wimberlyw/ardumiibo/Game/TurboWaddle/characters.h

 //this contains the sprite arrays
#include <Arduboy2.h>

// IMAGES FOR RUNNING MAN

const uint8_t PROGMEM runningman[] = 
{
  16,16,
  //FRAME 1
  0x00, 0x00, 0xc0, 0xe0, 0x70, 0x30, 0x30, 0x30, 0xe0, 0xe0, 0xfc, 0x3c, 0x34, 0xbc, 0xc0, 0xc0, 
  0x0c, 0x1c, 0x38, 0x30, 0x30, 0x38, 0x1c, 0x0e, 0x07, 0x03, 0x0f, 0x1f, 0x3b, 0x71, 0xe1, 0xc0, 
   //FRAME 2
  0x00, 0x00, 0x00, 0x00, 0x00, 0xe0, 0xf0, 0xb0, 0xf0, 0xfc, 0x3c, 0xb4, 0xbc, 0x00, 0x00, 0x00, 
  0x00, 0x00, 0x00, 0x18, 0x38, 0x30, 0x39, 0x1d, 0x0f, 0x07, 0x0f, 0x1f, 0xf9, 0xf0, 0x00, 0x00, 
   //FRAME 3
  0x00, 0x00, 0x00, 0x00, 0x00, 0x00, 0x80, 0xc0, 0xfc, 0xfc, 0xb4, 0x3c, 0x00, 0x00, 0x00, 0x00, 
  0x00, 0x00, 0x00, 0x00, 0x00, 0x00, 0x00, 0x01, 0xff, 0xff, 0x7b, 0x33, 0x00, 0x00, 0x00, 0x00, 
   //FRAME 4
  0x00, 0x00, 0x00, 0x00, 0xc0, 0xe0, 0x70, 0x30, 0xf0, 0xfc, 0x3c, 0xb4, 0xfc, 0xc0, 0x00, 0x00, 
  0x00, 0x00, 0xc0, 0xe0, 0x70, 0x38, 0x1c, 0x0e, 0x07, 0x03, 0x03, 0x07, 0x0f, 0x1c, 0x38, 0x60, 
  //JUMP FRAME
  0x00, 0x00, 0x00, 0x00, 0x00, 0x00, 0x00, 0x80, 0xe0, 0xf0, 0xfc, 0x7f, 0x37, 0x3e, 0x07, 0x03, 
  0x30, 0x38, 0x1c, 0xcc, 0xee, 0x77, 0x3b, 0x1f, 0x0f, 0x07, 0x01, 0x00, 0x00, 0x00, 0x00, 0x00, 
};

const uint8_t PROGMEM beefball[] = 
{
  16, 16,
  //FRAME 1
  0x00, 0x40, 0x80, 0xd0, 0xe0, 0x60, 0x20, 0x20, 0xb0, 0x20, 0x60, 0x60, 0xc0, 0xa0, 0x00, 0x00, 
  0x84, 0x7f, 0xff, 0xc1, 0x80, 0x84, 0x8e, 0x98, 0x91, 0x90, 0x8b, 0x80, 0xc0, 0xe1, 0x3f, 0x48, 
  //FRAME 2
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
};

class PlayerOne
{

  public:
    //Vars
    String selectedChar;
    int posY;
    int posX;
    int shield;
    int animStep;
    bool canJump;
    
    //Functions
    PlayerOne(void);
    const uint8_t PROGMEM *getSpriteSet(String);

   
    
};
