wimberlyw/ardumiibo/Game/TurboWaddle/menus.h

#include <Arduboy2.h>


const uint8_t PROGMEM intro[] = {
  64, 32,
  0x80, 0xc0, 0xe0, 0x60, 0x70, 0x30, 0x30, 0x30, 0x70, 0xf0, 0xf0, 0xf0, 0x30, 0x38, 0x18, 0x18, 0x18, 0x18, 0x1c, 0x0c, 0x0c, 0x40, 0xc0, 0xc0, 0x00, 0x00, 0xf0, 0xf8, 0xdc, 0xcc, 0xfc, 0xfc, 0x98, 0x80, 0x00, 0x06, 0x1f, 0x7f, 0xf3, 0xe3, 0x73, 0x3f, 0x3e, 0x30, 0x70, 0xf0, 0xe0, 0x00, 0xf0, 0xfe, 0xfe, 0x0e, 0x86, 0x86, 0xfe, 0xfe, 0x7c, 0x00, 0x80, 0x80, 0x00, 0x00, 0x00, 0x00, 
  0x03, 0x07, 0x0e, 0x0e, 0x0f, 0x07, 0x00, 0x00, 0x00, 0x00, 0x03, 0x07, 0x1f, 0x7c, 0xf0, 0xc0, 0x03, 0x1f, 0x1e, 0xb8, 0xb0, 0xb0, 0xb1, 0x3f, 0x1f, 0x00, 0x00, 0x83, 0x87, 0x9f, 0x9c, 0x80, 0x81, 0x83, 0x87, 0x86, 0x00, 0x70, 0xf3, 0xf7, 0xf7, 0x36, 0x36, 0x76, 0x67, 0xe7, 0xc3, 0xb0, 0x70, 0xf3, 0xc3, 0x03, 0x03, 0x1b, 0x39, 0x7c, 0xee, 0xe7, 0xf3, 0x3b, 0x38, 0x18, 0x00, 0x00, 
  0x00, 0x80, 0xc0, 0xe0, 0xe0, 0x60, 0xe0, 0xc0, 0x00, 0x00, 0x00, 0x00, 0x00, 0x00, 0x0c, 0x1c, 0x3c, 0xf8, 0xe0, 0x8f, 0x3f, 0xff, 0xe3, 0xc7, 0xde, 0xfc, 0x70, 0xe1, 0xe7, 0x8f, 0x19, 0x71, 0xe1, 0xc1, 0x83, 0x87, 0xff, 0xfc, 0xf0, 0x03, 0x0f, 0x1e, 0x78, 0xe0, 0xc0, 0xe0, 0x7f, 0x3f, 0x00, 0x03, 0x07, 0x1f, 0xfc, 0xf0, 0xe0, 0x70, 0x70, 0x33, 0x07, 0x1e, 0x1c, 0x1c, 0x0f, 0x07, 
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
    void CharacterSelect(Arduboy2, String *characters, bool *unlocks, int, int);
    bool ScanMenu(Arduboy2 ab, String *characters, bool *unlocks, int x, int y);
    bool openEgg(Arduboy2 ab, int x, int y);
    int swoosValue(int frame, bool negative);
};
