wimberlyw/ardumiibo/Scanner Programs/NFCReader/NFCReader.ino

#include <Wire.h>

#include <PN532_I2C.h>

#include <PN532.h>

#include <NfcAdapter.h>
PN532_I2C pn532_i2c(Wire);

#include <Adafruit_NeoPixel.h>
#define LED_PIN    4
#define LED_COUNT 24




String finalpayload = "";

NfcAdapter nfc = NfcAdapter(pn532_i2c);

Adafruit_NeoPixel strip(LED_COUNT, LED_PIN, NEO_GRB + NEO_KHZ800);
// Argument 1 = Number of pixels in NeoPixel strip
// Argument 2 = Arduino pin number (most are valid)
// Argument 3 = Pixel type flags, add together as needed:
//   NEO_KHZ800  800 KHz bitstream (most NeoPixel products w/WS2812 LEDs)
//   NEO_KHZ400  400 KHz (classic 'v1' (not v2) FLORA pixels, WS2811 drivers)
//   NEO_GRB     Pixels are wired for GRB bitstream (most NeoPixel products)
//   NEO_RGB     Pixels are wired for RGB bitstream (v1 FLORA pixels, not v2)
//   NEO_RGBW    Pixels are wired for RGBW bitstream (NeoPixel RGBW products)

String Message;

void setup() {
  
  Serial1.begin(115200);
  delay(100);
  nfc.begin();
  //Serial1.println("on");
  delay(1000);
  //Serial1.println("Scan your Arduumiibo");
  //delay(3000);
  strip.begin();           // INITIALIZE NeoPixel strip object (REQUIRED)
  strip.show();            // Turn OFF all pixels ASAP
  strip.setBrightness(50); // Set BRIGHTNESS to about 1/5 (max = 255)
}

void loop() {
    
    theaterChase(strip.Color(  0,   0, 127), 50); // Blue, half brightness
    if (nfc.tagPresent())
    {
       NfcTag tag = nfc.read();
    if (tag.hasNdefMessage()) // If your tag has a message
    {

      NdefMessage message = tag.getNdefMessage();
      /*Serial.print("\nThis Message in this Tag is ");
      Serial.print(message.getRecordCount());
      Serial.print(" NFC Tag Record");
      if (message.getRecordCount() != 1) { 
        //Serial.print("s");
      }
      Serial.println(".");
      */
      // If you have more than 1 Message then it wil cycle through them
      int recordCount = message.getRecordCount();
      for (int i = 0; i < recordCount; i++)
      {
        Serial.print("\nNDEF Record ");Serial.println(i+1);
        NdefRecord record = message.getRecord(i);

        int payloadLength = record.getPayloadLength();
        byte payload[payloadLength];
        record.getPayload(payload);


        String payloadAsString = ""; // Processes the message as a string vs as a HEX value
        
        for (int c = 0; c < payloadLength; c++) {
          
          payloadAsString += (char)payload[c];
          
          
          
        }
        //Serial.print("  Information (as String): ");
        
        Serial1.println(payloadAsString);
        colorWipe(strip.Color(  0, 255,   0), 50); // Green
        delay(500);
        theaterChase(strip.Color(  0,   127, 0), 25); // green, half brightness
        rainbow(3);             // Flowing rainbow cycle along the whole strip
        delay(1000);            //duration 2 seconds
       // Serial1.println("Ending Link");
        delay(1000);
        Serial1.flush();
        
        //Serial1.println("off");
        //Serial1.end();
/*
        String uid = record.getId();
        if (uid != "") {
          Serial.print("  ID: ");Serial.println(uid); // Prints the Unique Identification of the NFC Tag
        }*/
      }
    }
 }
}

// Some functions of our own for creating animated effects -----------------

// Fill strip pixels one after another with a color. Strip is NOT cleared
// first; anything there will be covered pixel by pixel. Pass in color
// (as a single 'packed' 32-bit value, which you can get by calling
// strip.Color(red, green, blue) as shown in the loop() function above),
// and a delay time (in milliseconds) between pixels.
void colorWipe(uint32_t color, int wait) {
  for (int i = 0; i < strip.numPixels(); i++) { // For each pixel in strip...
    strip.setPixelColor(i, color);         //  Set pixel's color (in RAM)
    strip.show();                          //  Update strip to match
    delay(wait);                           //  Pause for a moment
  }
}

// Theater-marquee-style chasing lights. Pass in a color (32-bit value,
// a la strip.Color(r,g,b) as mentioned above), and a delay time (in ms)
// between frames.
void theaterChase(uint32_t color, int wait) {
  for (int a = 0; a < 10; a++) { // Repeat 10 times...
    for (int b = 0; b < 3; b++) { //  'b' counts from 0 to 2...
      strip.clear();         //   Set all pixels in RAM to 0 (off)
      // 'c' counts up from 'b' to end of strip in steps of 3...
      for (int c = b; c < strip.numPixels(); c += 3) {
        strip.setPixelColor(c, color); // Set pixel 'c' to value 'color'
      }
      strip.show(); // Update strip with new contents
      delay(wait);  // Pause for a moment
    }
  }
}

// Rainbow cycle along whole strip. Pass delay time (in ms) between frames.
void rainbow(int wait) {
  // Hue of first pixel runs 5 complete loops through the color wheel.
  // Color wheel has a range of 65536 but it's OK if we roll over, so
  // just count from 0 to 5*65536. Adding 256 to firstPixelHue each time
  // means we'll make 5*65536/256 = 1280 passes through this outer loop:
  for (long firstPixelHue = 0; firstPixelHue < 5 * 65536; firstPixelHue += 256) {
    for (int i = 0; i < strip.numPixels(); i++) { // For each pixel in strip...
      // Offset pixel hue by an amount to make one full revolution of the
      // color wheel (range of 65536) along the length of the strip
      // (strip.numPixels() steps):
      int pixelHue = firstPixelHue + (i * 65536L / strip.numPixels());
      // strip.ColorHSV() can take 1 or 3 arguments: a hue (0 to 65535) or
      // optionally add saturation and value (brightness) (each 0 to 255).
      // Here we're using just the single-argument hue variant. The result
      // is passed through strip.gamma32() to provide 'truer' colors
      // before assigning to each pixel:
      strip.setPixelColor(i, strip.gamma32(strip.ColorHSV(pixelHue)));
    }
    strip.show(); // Update strip with new contents
    delay(wait);  // Pause for a moment
  }
}
