wimberlyw/ardumiibo/Examples/ScanDemo/sprites.h

#pragma once

const uint8_t PROGMEM GL0[] = {
32, 32,
0x00, 0x00, 0x00, 0xc0, 0xb0, 0x50, 0x1c, 0x0e, 0x82, 0x22, 0xb2, 0x02, 0x02, 0x02, 0x04, 0x08, 0x08, 0xf0, 0x80, 0x00, 0x00, 0x00, 0x00, 0x00, 0x00, 0x00, 0x00, 0x00, 0x00, 0x00, 0x00, 0x00, 
0x80, 0x40, 0x80, 0x41, 0x46, 0x40, 0x45, 0x7d, 0x7d, 0x1d, 0x01, 0x81, 0x01, 0x00, 0x04, 0xde, 0xde, 0xfa, 0xf8, 0xd7, 0xc0, 0xbc, 0x20, 0xc0, 0x00, 0x00, 0x00, 0x00, 0x00, 0x00, 0x00, 0x00, 
0x07, 0x08, 0x0b, 0x1c, 0x14, 0xe8, 0x08, 0x08, 0x08, 0x08, 0x8c, 0x03, 0x00, 0x00, 0x00, 0x01, 0x01, 0x0b, 0xf7, 0xf5, 0x25, 0x03, 0x7c, 0x83, 0x00, 0x00, 0x00, 0x00, 0x00, 0x00, 0x00, 0x00, 
0x00, 0x00, 0x00, 0x00, 0x00, 0x01, 0xc6, 0x24, 0xba, 0xc1, 0x00, 0x00, 0x00, 0xc2, 0xf8, 0xc0, 0xc0, 0x80, 0x80, 0x8e, 0x1d, 0x1a, 0x08, 0x21, 0x36, 0x28, 0x38, 0x30, 0xe0, 0x00, 0x00, 0x00, 

0x00, 0x00, 0x00, 0xc0, 0xb0, 0x50, 0x1c, 0x0e, 0x82, 0x22, 0xb2, 0x02, 0x02, 0x02, 0x04, 0x08, 0x08, 0xf0, 0x80, 0x00, 0x00, 0x00, 0x00, 0x00, 0x00, 0x00, 0x00, 0x00, 0x00, 0x00, 0x00, 0x00, 
0x80, 0x40, 0x80, 0x41, 0x46, 0x40, 0x45, 0x7d, 0x7d, 0x1d, 0x01, 0x81, 0x01, 0x00, 0x04, 0xde, 0xde, 0xfa, 0xf8, 0xd7, 0xc0, 0xbc, 0x20, 0xc0, 0x00, 0x00, 0x00, 0x00, 0x00, 0x00, 0x00, 0x00, 
0x07, 0x08, 0x0b, 0x1c, 0x14, 0xe8, 0x08, 0x08, 0x08, 0x08, 0x8c, 0x03, 0x00, 0x00, 0x00, 0x01, 0x01, 0x0b, 0xf7, 0xf5, 0x25, 0x03, 0x7c, 0x83, 0x00, 0x00, 0x00, 0x00, 0x00, 0x00, 0x00, 0x00, 
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
8,8,

0x1c, 0x3e, 0x7e, 0xfc, 0xfc, 0x7e, 0x3e, 0x1c, 
};

const uint8_t PROGMEM doa[] = {
16, 16,
0xf4, 0x0a, 0x35, 0xf5, 0xf5, 0xf5, 0xf5, 0xf5, 0xf5, 0xf5, 0xf5, 0xf5, 0xf5, 0x0d, 0xfa, 0xfc, 
0xff, 0x00, 0xf3, 0xff, 0xff, 0xff, 0xff, 0xff, 0xff, 0xff, 0xf9, 0xf9, 0xff, 0x00, 0xff, 0xff, 
};
